Brautantoine/gr-iut/CAO/MECA/source/Jonction/jonction_haut.SLDPRT

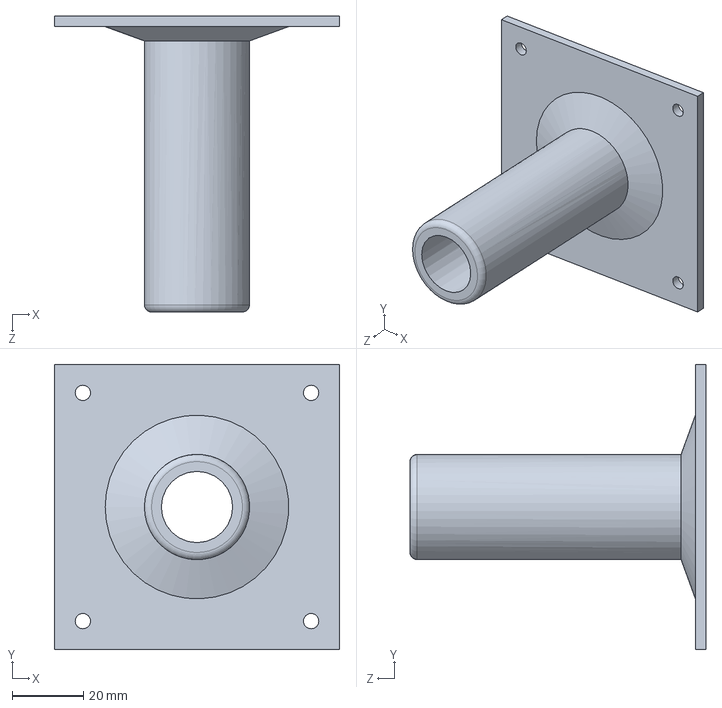
[picture p20: CAD file, 2019-06-02]
CAO/MECA/source/Jonction/jonction_haut.SLDPRT
80.0 x 80.0 x 83.0 mm
