Brautantoine/gr-iut/CAO/MECA/source/Tour/triangle_base.SLDPRT

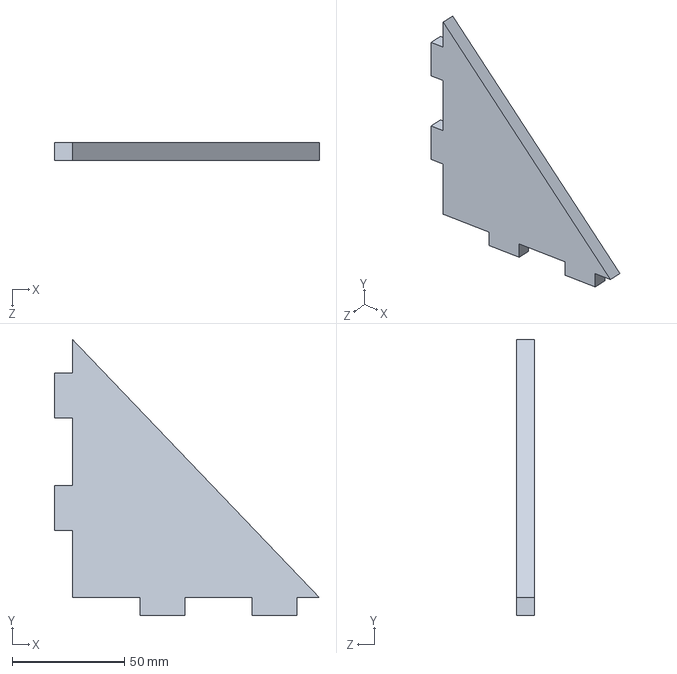
[picture p21: CAD file, 2019-06-02]
CAO/MECA/source/Tour/triangle_base.SLDPRT
118.0 x 123.0 x 8.00 mm
