Brautantoine/gr-iut/CAO/MECA/Output/base_dessus.DXF

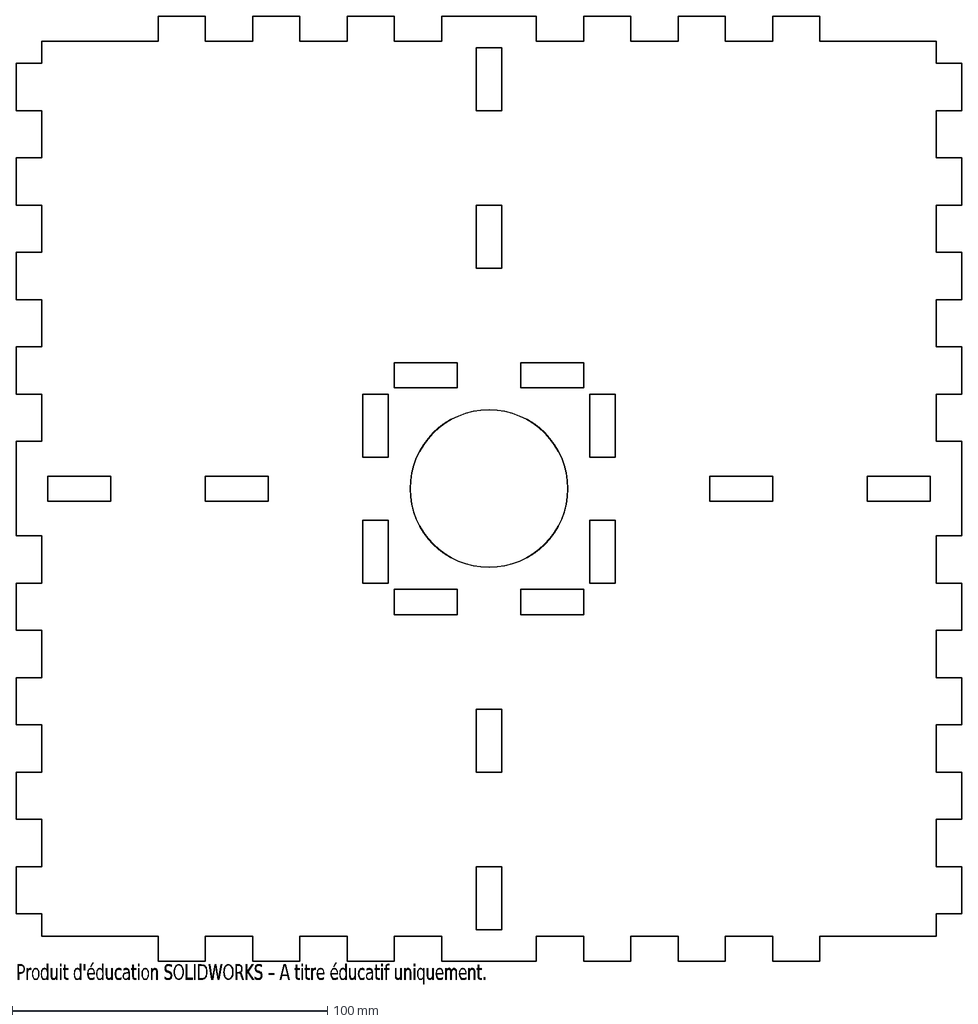
[picture p22: CAD file, 2019-06-02]
CAO/MECA/Output/base_dessus.DXF
Produit d'éducation SOLIDWORKS – A titre éducatif uniquement.
