Brautantoine/gr-iut/CAO/MECA/source/Base/tete_base.SLDPRT

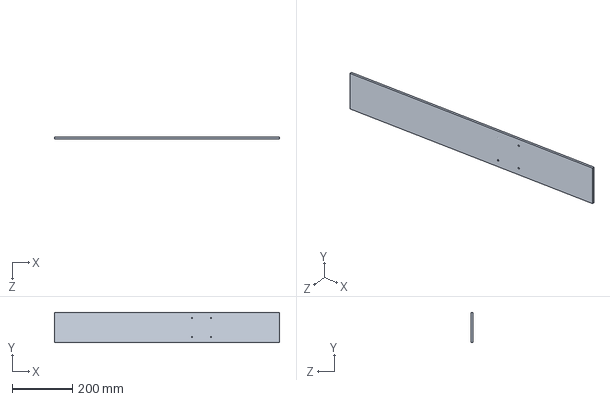
[picture p23: CAD file, 2019-06-02]
CAO/MECA/source/Base/tete_base.SLDPRT
750.0 x 100.0 x 6.00 mm
