Brautantoine/gr-iut/CAO/MECA/Output/lateral.DXF

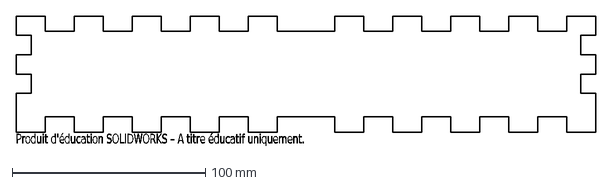
[picture p24: CAD file, 2019-06-02]
CAO/MECA/Output/lateral.DXF
Produit d'éducation SOLIDWORKS – A titre éducatif uniquement.
