Brautantoine/gr-iut/CAO/MECA/source/Base/latéral_1.SLDPRT

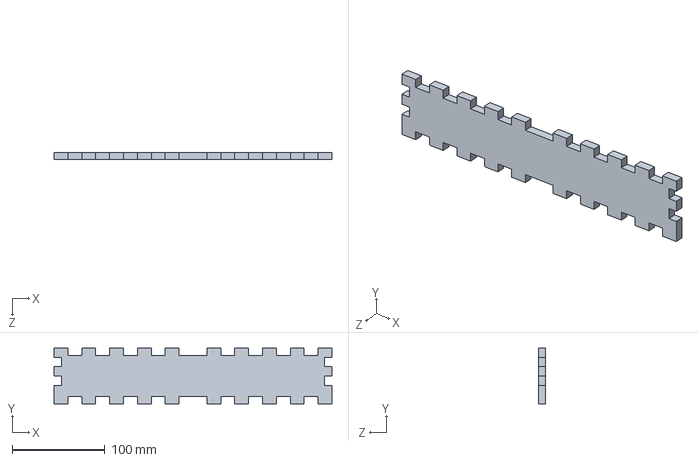
[picture p25: CAD file, 2019-06-02]
CAO/MECA/source/Base/latéral_1.SLDPRT
300.0 x 60.0 x 8.00 mm
