Brautantoine/gr-iut/CAO/MECA/Output/base_socle.DXF

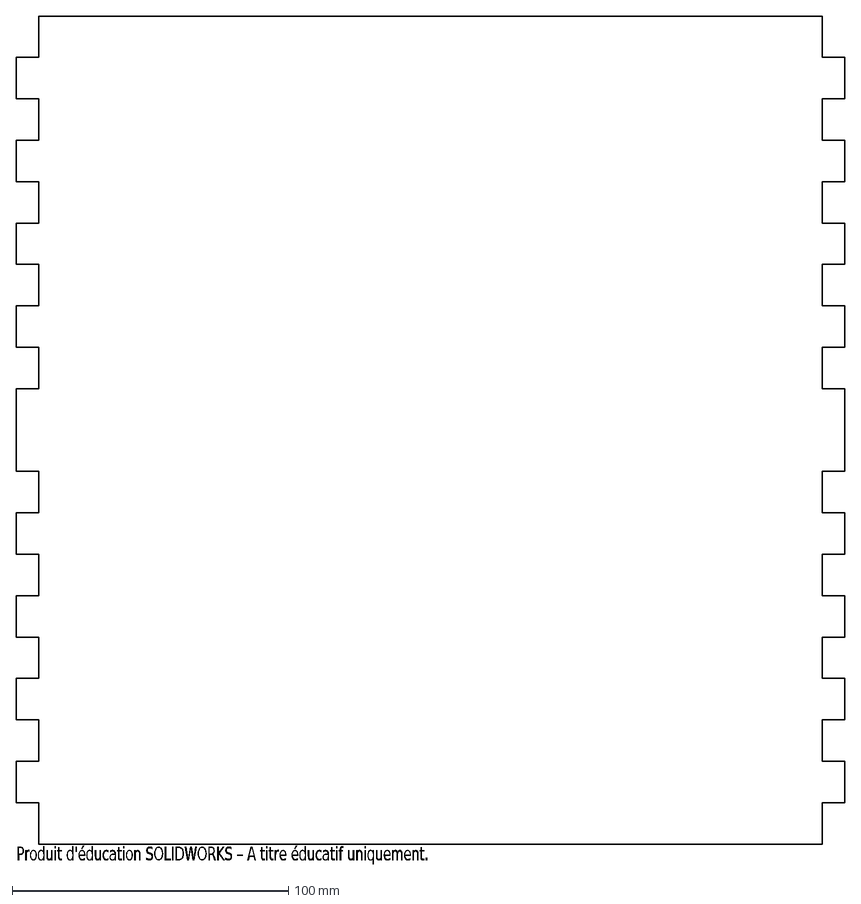
[picture p26: CAD file, 2019-06-02]
CAO/MECA/Output/base_socle.DXF
Produit d'éducation SOLIDWORKS – A titre éducatif uniquement.
