Brautantoine/gr-iut/CAO/MECA/source/Base/arriere.SLDPRT

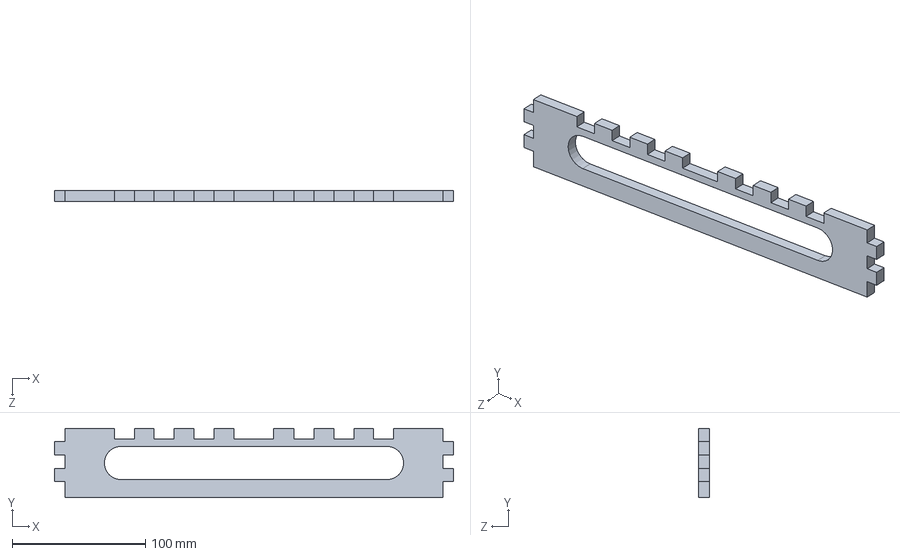
[picture p27: CAD file, 2019-06-02]
CAO/MECA/source/Base/arriere.SLDPRT
300.0 x 52.0 x 8.00 mm
