Brautantoine/gr-iut/CAO/MECA/Output/arriere.DXF

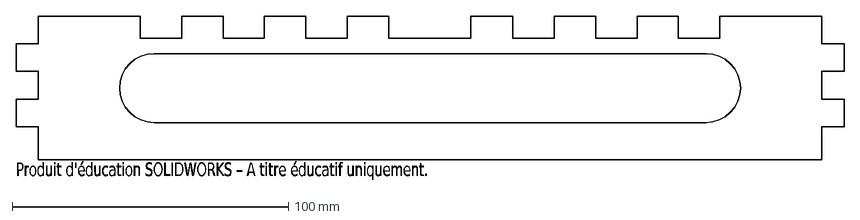
[picture p28: CAD file, 2019-06-02]
CAO/MECA/Output/arriere.DXF
Produit d'éducation SOLIDWORKS – A titre éducatif uniquement.
