Brautantoine/gr-iut/CAO/MECA/Output/avant.DXF

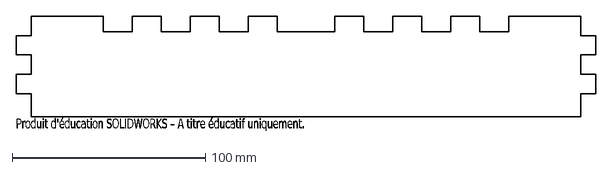
[picture p29: CAD file, 2019-06-02]
CAO/MECA/Output/avant.DXF
Produit d'éducation SOLIDWORKS – A titre éducatif uniquement.
