Brautantoine/gr-iut/CAO/MECA/Output/tour_lateral.DXF

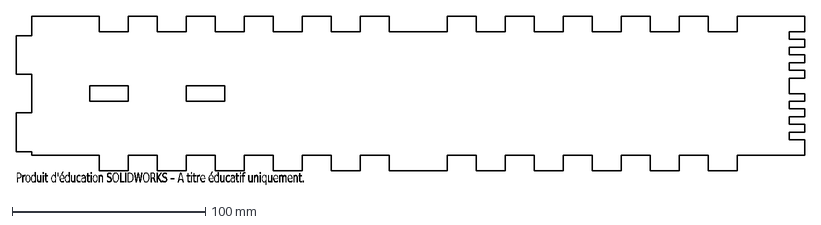
[picture p30: CAD file, 2019-06-02]
CAO/MECA/Output/tour_lateral.DXF
Produit d'éducation SOLIDWORKS – A titre éducatif uniquement.
